lorenzfischer/spacebar_led/3d_objects/electronics_platform.v13.tp4056.stl

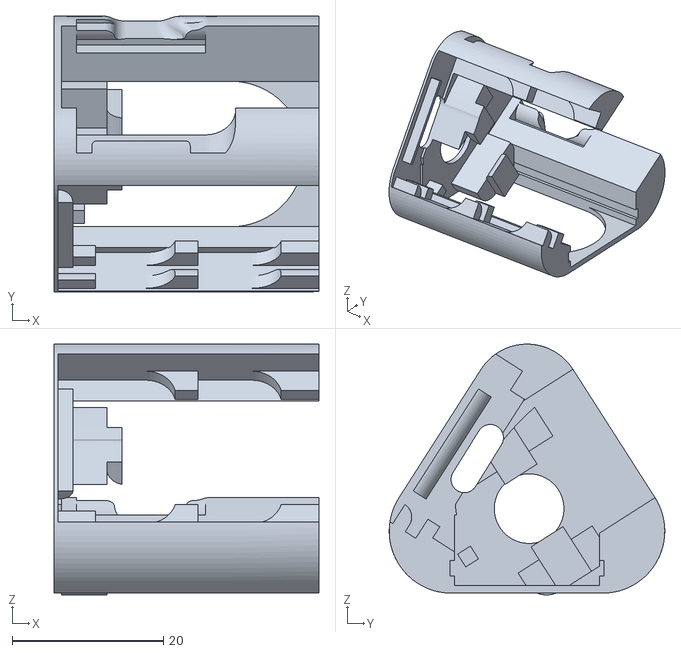
[picture p19: CAD file, 2022-08-22]
3d_objects/electronics_platform.v13.tp4056.stl
35.0 x 36.4 x 33.1
