lorenzfischer/spacebar_led/3d_objects/lid.v2.with_hole.stl

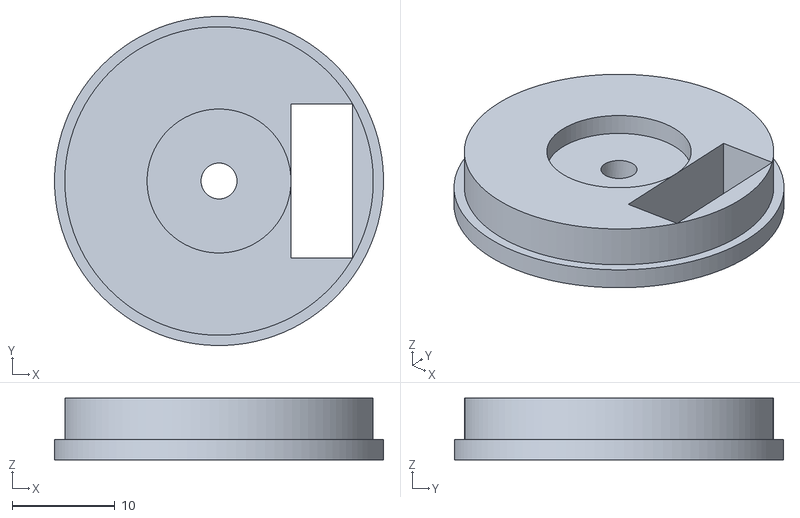
[picture p21: CAD file, 2022-03-22]
3d_objects/lid.v2.with_hole.stl
32.0 x 32.0 x 6.00
